ZeekiChen/iWatch/v1.2/CODE/iWatch-v1.2-20201225/User/Page/page_setting.c

#include "iWatch.h"

extern unsigned char xdata main_cache[];
extern unsigned char xdata sub_cache[];

static PageExecuteRate_TypeDef Rate_50hz = {20, 0};

static unsigned char code Text[] = "SETTING";
static unsigned char code Icon[] = {
0x00,0x00,0x00,0x00,0x00,0x00,0x00,0x00,0x00,0x80,0xC0,0xC0,0xC0,0x80,0x00,0x00,
0x00,0x00,0x00,0xE0,0xFC,0xFC,0x1C,0x0C,0x0C,0x1C,0xFC,0xFC,0xC0,0x00,0x00,0x00,
0x00,0x00,0x80,0xC0,0xC0,0xC0,0x80,0x00,0x00,0x00,0x00,0x00,0x00,0x00,0x00,0x00,
0x00,0x00,0x00,0x00,0x00,0x00,0x0C,0x1E,0x7F,0xF7,0xE3,0x81,0x03,0x03,0x07,0x0E,
0x0E,0x07,0x07,0x03,0x83,0x81,0x80,0x80,0x80,0x80,0x81,0x83,0x03,0x07,0x07,0x0E,
0x0E,0x07,0x03,0x03,0x81,0xE3,0xF7,0x7F,0x1E,0x0C,0x00,0x00,0x00,0x00,0x00,0x00,
0x00,0x00,0xF0,0xF0,0x70,0x38,0x38,0x38,0x3E,0x3F,0x0F,0x01,0x00,0x00,0x00,0xF0,
0xFC,0x7E,0x0F,0x07,0xC3,0xE3,0xF1,0x71,0x71,0xF1,0xE3,0xC3,0x07,0x0F,0x7E,0xFC,
0xF0,0x00,0x00,0x00,0x01,0x0F,0x3F,0x3E,0x38,0x38,0x38,0x70,0xF0,0xF0,0x00,0x00,
0x00,0x00,0x0F,0x0F,0x0E,0x0C,0x0C,0x1C,0x7C,0xFC,0xF0,0xC0,0x00,0x00,0x00,0x07,
0x1F,0x3E,0x78,0xF0,0xE1,0xC7,0xC7,0xCE,0xCE,0xC7,0xC7,0xE1,0xE0,0x78,0x3E,0x1F,
0x07,0x00,0x00,0x00,0xC0,0xF0,0xFC,0x7C,0x1C,0x0C,0x0C,0x0E,0x0F,0x0F,0x00,0x00,
0x00,0x00,0x00,0x00,0x00,0x00,0x30,0x7C,0xFE,0xEF,0xC7,0x81,0xC0,0xE0,0xE0,0x70,
0x70,0xF0,0xE0,0xE0,0xC0,0xC1,0x01,0x01,0x01,0x01,0xC1,0xC0,0xE0,0xE0,0xF0,0x70,
0x70,0xE0,0xE0,0xC0,0x81,0xC7,0xEF,0xFE,0x7C,0x30,0x00,0x00,0x00,0x00,0x00,0x00,
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
		0x00,0x00,0x10,0x11,0x16,0x10,0x10,0xF0,0x10,0x10,0x14,0x13,0x10,0x00,0x00,0x00,
		0x10,0x10,0xD0,0xFF,0x90,0x10,0x00,0xFE,0x02,0x02,0x02,0xFE,0x00,0x00,0x00,0x00,
		0x00,0x80,0x80,0x80,0x80,0x80,0x80,0x80,0x80,0x80,0x80,0x80,0x80,0x80,0x00,0x00,
		0x00,0x00,0x00,0x00,0x00,0x00,0x00,0x00,0x00,0x00,0x00,0x00,0x00,0x00,0x00,0x00,
		0x81,0x81,0x41,0x41,0x21,0x11,0x0D,0x03,0x0D,0x11,0x21,0x41,0x41,0x81,0x81,0x00,
		0x04,0x03,0x00,0xFF,0x00,0x83,0x60,0x1F,0x00,0x00,0x00,0x3F,0x40,0x40,0x78,0x00,
		0x00,0x00,0x00,0x00,0x00,0x00,0x00,0x00,0x00,0x00,0x00,0x00,0x00,0x00,0x00,0x00
		/* (64 X 16 )*/
	}
};
#define	MENU_MAX_INDEX	sizeof(SETTINGMENU)/(64*16/8)
static unsigned char code TICK_CROSS[2][32] = {
	{
		0x00,0x0C,0x1E,0x3E,0x7C,0xF8,0xF0,0xE0,0xE0,0xF0,0xF8,0x7C,0x3E,0x1E,0x0C,0x00,
		0x00,0x38,0x7C,0x7E,0x3F,0x1F,0x0F,0x07,0x07,0x0F,0x1F,0x3E,0x7C,0x78,0x30,0x00
		/* (16 X 16 )*/
	},
	{
		0x00,0x80,0xC0,0x80,0x00,0x00,0x00,0x00,0x80,0xC0,0xE0,0xF0,0xF8,0xFC,0x7C,0x38,
		0x03,0x07,0x0F,0x1F,0x3F,0x7E,0x7E,0x3F,0x1F,0x0F,0x07,0x03,0x01,0x00,0x00,0x00
		/* (16 X 16 )*/
	}
};

void SetTime(void);

extern iWatch_config config;	//设置信息结构体
static char menu_first_index = 0;
static char menu_now_index = 0;
static bit selected = 0;
static selected_index = 0;

#define	SWITCH	0
#define	NUM			1
#define	EXE			2
typedef void(*SettingExecute_t)(unsigned char);
typedef void(*SettingExecute)(void);
typedef struct {
	unsigned char *item_content;		//设置项目的文本/图片的指针
	unsigned char control_type;			//设置的类型，NUM:更改数值，SWITCH:开关型，EXE:直接执行型
	unsigned char *value;						//被设置的值的指针
	SettingExecute_t SettingExe_t;	//有一个参数的执行函数，NUM和SWITCH设置类型的属性
	SettingExecute	 SettingExe;		//没有参数的执行函数，EXE设置类型才有的属性
	unsigned char step;							//NUM设置类型的数值步进长度
	unsigned char value_max;					//NUM设置类型的数值最大值
	unsigned char value_min;					//NUM设置类型的数值最小值
	unsigned char *unit;						//被设置的值的单位字符串的指针，NUM设置类型才有的属性
}Setting_TypeDef;
static Setting_TypeDef menu_item[] = {
	{SETTINGMENU[0], EXE, 	 0, 0,										SetTime},
	{SETTINGMENU[1], NUM, 	 0, 0,										0,							1,  20,  5,  "s"},
	{SETTINGMENU[2], NUM, 	 0,	ScreenSetBrightness,	0,							10, 100, 10, "%"},
	{SETTINGMENU[3], SWITCH, 0, 0,										0},
	{SETTINGMENU[4], SWITCH, 0, 0,										0},
	{SETTINGMENU[5], SWITCH, 0,	ScreenSetInverse,			0},
	{SETTINGMENU[6], SWITCH, 0,	EnableBuzzer,					0},
	{SETTINGMENU[7], EXE,		 0,	0, 										MCUSoftReset},
	{SETTINGMENU[8], EXE, 	 0, 0,										iWatchPowerDown}
};		

/**
  * @brief  页面初始化事件
  * @param  无
  * @retval 无
  */
static void Setup()
{
	unsigned char i;
	ClearCache(sub_cache);
	menu_item[1].value = &config.t_inactive_max;
	menu_item[2].value = &config.screen_brightness;
	menu_item[3].value = &config.wrist_up_wake;
	menu_item[4].value = &config.always_on_disp;
	menu_item[5].value = &config.screen_inverse;
	menu_item[6].value = &config.key_sound;
	for(i = 0; i < 4; i++)
	{
		BMPToCache(16, i * 2, 64, 16, menu_item[menu_first_index + i].item_content, sub_cache, COVER);
	}
	PageOpenAnim(ANIM_RIGHT);
}
/**
  * @brief  页面退出事件
  * @param  无
  * @retval 无
  */
static void Exit()
{
	iWatchSaveConfig(&config);
	PageCloseAnim(ANIM_RIGHT);
}
/**
  * @brief  页面循环执行的内容
  * @param  无
  * @retval 无
  */
static void Loop()
{	unsigned char i;
	unsigned char str[5];
	if(PageExecuteRate(&Rate_50hz) == 1)
	{
		ClearCache(main_cache);
		for(i = 0; i < 4; i++)
		{
			BMPToCache(16, i * 2, 64, 16, menu_item[menu_first_index + i].item_content, main_cache, COVER);
			if(menu_item[menu_first_index + i].control_type == SWITCH)
				BMPToCache(96, i * 2, 16, 16, TICK_CROSS[*menu_item[menu_first_index + i].value], main_cache, COVER);
			else if(menu_item[menu_first_index + i].control_type == NUM)
			{
				sprintf(str, "%d%s", (int)(*menu_item[menu_first_index + i].value), (char*)menu_item[menu_first_index + i].unit);
				ShowString(96, i * 2, str, main_cache, FONT8X16, (selected&&selected_index==menu_first_index + i)?INVERSED:NO_INVERSED);
			}
		}
		ShowString(0, (menu_now_index - menu_first_index) * 2, ">", main_cache, FONT8X16, NO_INVERSED);
		ScreenRefreshAll(main_cache);
	}
	
}
/**
  * @brief  页面事件
  * @param  btn:发出事件的按键
  * @param  event:事件编号
  * @retval 无
  */
static void Event(unsigned char event)
{
	if(!selected)
	{
		if(event == KEY1)
			PageShift(page_menu);
		else if(event == KEY2)
		{
			if(--menu_now_index >= 0)
			{
				if(menu_now_index < menu_first_index)
					menu_first_index--;
			}
			else
				menu_now_index = 0;
		}
		else if(event == KEY3)
		{
			if(++menu_now_index < MENU_MAX_INDEX)
			{
				if(menu_now_index > menu_first_index + 3)
					++menu_first_index;
			}
			else
				menu_now_index = MENU_MAX_INDEX - 1;
		}
		else if(event == DOUBLE_TAP)
		{
			if(menu_item[menu_now_index].control_type == SWITCH)
			{
				*menu_item[menu_now_index].value = !*menu_item[menu_now_index].value;
				if(menu_item[menu_now_index].SettingExe_t != 0)
					menu_item[menu_now_index].SettingExe_t(*menu_item[menu_now_index].value);
			}
			else if(menu_item[menu_now_index].control_type == EXE)
			{
				if(menu_item[menu_now_index].SettingExe != 0)
					menu_item[menu_now_index].SettingExe();
			}
			else if(menu_item[menu_now_index].control_type == NUM)
			{
				selected = 1;
				selected_index = menu_now_index;
			}
		}
	}
	else
	{
		if(event == KEY1)
			selected = 0;
		else if(event == KEY2)
		{
			*menu_item[menu_now_index].value += menu_item[menu_now_index].step;
			if(*menu_item[menu_now_index].value >= menu_item[menu_now_index].value_max)
				*menu_item[menu_now_index].value = menu_item[menu_now_index].value_max;
		}
		else if(event == KEY3)
		{
			*menu_item[menu_now_index].value -= menu_item[menu_now_index].step;
			if(*menu_item[menu_now_index].value <= menu_item[menu_now_index].value_min)
				*menu_item[menu_now_index].value = menu_item[menu_now_index].value_min;
		}
		if(menu_item[menu_now_index].SettingExe_t != 0)
			menu_item[menu_now_index].SettingExe_t(*menu_item[menu_now_index].value);
	}
}

void PageRegister_page_setting(unsigned char pageID)
{
	PageRegister(pageID, Text, Icon, Setup, Loop, Exit, Event);
}
void SetTime(void)
{
	PageShift(page_settime);
}
