ZeekiChen/iWatch/v1.2/CODE/iWatch-v1.2-20201225/User/Page/page_bme280.c

#include "iWatch.h"

extern unsigned char xdata main_cache[];
extern unsigned char xdata sub_cache[];

static PageExecuteRate_TypeDef Rate_50hz = {20, 0};

static unsigned char code Text[] = "BME280";
static unsigned char code Icon[] = {
0x00,0x00,0x00,0x00,0x00,0xE0,0x70,0x10,0x18,0x18,0x18,0x10,0x70,0xE0,0x00,0x00,
0x00,0x00,0x00,0x00,0x00,0x00,0x30,0x60,0xC0,0x80,0x00,0x08,0xB8,0x80,0x80,0xC0,
0xDF,0xCE,0xC0,0x80,0x90,0x38,0x08,0x00,0xC0,0xE0,0x70,0x20,0x00,0x00,0x00,0x00,
0x00,0x00,0x00,0x00,0xFF,0xFF,0x98,0x98,0x18,0x18,0x18,0x00,0x00,0xFF,0xFF,0x00,
0x00,0x00,0xC0,0xC0,0xC4,0xC4,0x0C,0x00,0xF0,0xFC,0x0E,0x03,0x01,0x01,0x00,0x00,
0x00,0x00,0x00,0x00,0x01,0x03,0x07,0x0E,0xF8,0xE0,0x04,0x8C,0xC6,0xC0,0xC0,0x80,
0x00,0x00,0x00,0x00,0xFF,0xFF,0x73,0x73,0x00,0x00,0x00,0x00,0x00,0xFF,0xFF,0x00,
0x00,0x00,0x00,0x00,0x18,0x18,0x08,0x80,0xC3,0x8F,0x18,0x30,0x60,0x40,0xC0,0xC0,
0xC0,0xC0,0xC0,0xC0,0x60,0x60,0x30,0x1C,0xCF,0x81,0x08,0x08,0x18,0x00,0x00,0x00,
0x00,0x00,0x00,0x80,0xFF,0x7F,0x0E,0x0E,0x00,0x00,0x00,0x00,0x00,0x7F,0xFF,0x80,
0x00,0x00,0x00,0x00,0x00,0x00,0x03,0x03,0x01,0x00,0x00,0x0C,0x0E,0x00,0x00,0x00,
0x3C,0x3C,0x00,0x00,0x02,0x0E,0x00,0x00,0x00,0x01,0x03,0x02,0x00,0x00,0x00,0x00,
0xF0,0xFE,0x07,0x01,0x00,0x00,0x00,0x00,0x00,0x00,0x00,0x00,0x00,0xC0,0x40,0x01,
0x03,0x1E,0xF8,0x00,0x00,0x00,0x00,0x00,0x00,0x00,0x00,0x00,0x00,0x00,0x00,0x00,
0x00,0x00,0x00,0x00,0x00,0x00,0x00,0x00,0x00,0x00,0x00,0x00,0x00,0x00,0x00,0x00,
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
}
/**
  * @brief  页面循环执行的内容
  * @param  无
  * @retval 无
  */
static void Loop()
{
	if(PageExecuteRate(&Rate_50hz) == 1)
	{
		BME280GetSensorData(&BME280);					//读BME280测量数据并显示
		altitude = 44330.77 * (1 - pow((BME280.pressure / 101500), 0.190263));
		ClearCache(main_cache);
		BMPToCache(0, 0, 48, 64, T_H_P_A, main_cache, 0);
		sprintf(str1, "%.1f", BME280.temperature);
		ShowString(48, 0, str1, main_cache, FONT8X16, NO_INVERSED);
		BMPToCache(84, 0, 16, 16, CELSIUS_ICON, main_cache, 0);
		sprintf(str1, "%.1f %%", BME280.humidity);
		ShowString(48, 2, str1, main_cache, FONT8X16, NO_INVERSED);
		sprintf(str1, "%ld Pa", (long)BME280.pressure);
		ShowString(48, 4, str1, main_cache, FONT8X16, NO_INVERSED);
		sprintf(str1, "%d m", (int)altitude);
		ShowString(48, 6, str1, main_cache, FONT8X16, NO_INVERSED);
		ScreenRefreshAll(main_cache);
	}
}
/**
  * @brief  页面事件
  * @param  btn:发出事件的按键
  * @param  event:事件编号
  * @retval 无
  */
static void Event(unsigned char event)
{
	if(event == KEY1)
		PageShift(page_menu);
}

void PageRegister_page_bme280(unsigned char pageID)
{
	PageRegister(pageID, Text, Icon, Setup, Loop, Exit, Event);
}
