ZeekiChen/iWatch/v1.2/CODE/iWatch-v1.2-20201225/User/Sensor/Ellipsoid fitting.c

#include "Ellipsoid fitting.h"
#include "stdio.h"
#include "string.h"
#include "math.h"

#define MATRIX_SIZE 6
//#define u8 unsigned char
float m_matrix[MATRIX_SIZE][MATRIX_SIZE + 1];	//系数矩阵
float final_solve[MATRIX_SIZE] = { 0 };				//方程组的解对应最小二乘椭球拟合中的，a，b，c，d，e，f，

float m_result[MATRIX_SIZE];
int N = 0;//计算累计的采样点次数的

//取绝对值
float Abs(float a)
{
	return a < 0 ? -a : a;
}

//把矩阵系数全部清除为0
void ResetMatrix(void)
{
	unsigned char row, column;
	for (row = 0; row < MATRIX_SIZE; row++)
	{
		for (column = 0; column < MATRIX_SIZE + 1; column++)
			m_matrix[row][column] = 0.0f;
	}
}

//把输入的数据先生成矩阵的元素的总和
void CalcData_Input(float x, float y, float z)
{
	float V[MATRIX_SIZE + 1];
	unsigned char row, column;
	N++;
	V[0] = y*y;
	V[1] = z*z;
	V[2] = x;
	V[3] = y;
	V[4] = z;
	V[5] = 1.0;
	V[6] = -x*x;
	//构建系数矩阵，并进行累加
	for (row = 0; row < MATRIX_SIZE; row++)
	{
		for (column = 0; column < MATRIX_SIZE + 1; column++)
		{
			m_matrix[row][column] += V[row] * V[column];
		}
	}
	//b向量是m_matrix[row][6]
}

//化简系数矩阵，把除以N带上
void CalcData_Input_average()
{
	unsigned char row, column;
	for (row = 0; row < MATRIX_SIZE; row++)
		for (column = 0; column < MATRIX_SIZE + 1; column++)
			m_matrix[row][column] /= N;
	//b向量是m_matrix[row][6]
}
//显示出来系数矩阵和增广矩阵[A|b]
/*
void DispMatrix(void)
{
	unsigned char row, column;
	for (row = 0; row < MATRIX_SIZE; row++)
	{
		for (column = 0; column < MATRIX_SIZE + 1; column++)
		{
			printf("%23f ", m_matrix[row][column]);
			if (column == MATRIX_SIZE - 1)
				printf("|");
		}
		printf("\r\n");
	}
	printf("\r\n\r\n");
}
*/
//交换两行元素位置
void Row2_swop_Row1(int row1, int row2)
{
	float tmp = 0;
	unsigned char column;
	for (column = 0; column < MATRIX_SIZE + 1; column++)
	{
		tmp = m_matrix[row1][column];
		m_matrix[row1][column] = m_matrix[row2][column];
		m_matrix[row2][column] = tmp;
	}
}

//用把row行的元素乘以一个系数k
void k_muiltply_Row(float k, int row)
{
	unsigned char column;
	for (column = 0; column < MATRIX_SIZE + 1; column++)
		m_matrix[row][column] *= k;
}

//用一个数乘以row1行加到row2行上去
void Row2_add_kRow1(float k, int row1, int row2)
{
	unsigned char column;
	for (column = 0; column < MATRIX_SIZE + 1; column++)
		m_matrix[row2][column] += k*m_matrix[row1][column];
}


//列主元，第k次消元之前，把k行到MATRIX_SIZE的所有行进行冒泡排出最大，排序的依据是k列的元素的大小
void MoveBiggestElement_to_Top(int k)
{
	int row = 0, column = 0;
	for (row = k + 1; row < MATRIX_SIZE; row++)
	{
		if (Abs(m_matrix[k][k]) < Abs(m_matrix[row][k]))
		{
			Row2_swop_Row1(k, row);
		}
	}
}

//高斯消元法，求行阶梯型矩阵
unsigned char Matrix_GaussElimination(void)
{
	float k = 0;
	unsigned char cnt,row;
	for (cnt = 0; cnt < MATRIX_SIZE; cnt++)//进行第k次的运算，主要是针对k行以下的行数把k列的元素都变成0
	{
		//把k行依据k列的元素大小，进行排序
		MoveBiggestElement_to_Top(cnt);
		if (m_matrix[cnt][cnt] == 0)
			return(1);			//返回值表示错误
		//把k行下面的行元素全部消成0，整行变化
		for (row = cnt + 1; row < MATRIX_SIZE; row++)
		{
			k = -m_matrix[row][cnt] / m_matrix[cnt][cnt];
			Row2_add_kRow1(k, cnt, row);
		}
		//DispMatrix();
	}
	return 0;
}

//求行最简型矩阵，即把对角线的元素全部化成1
void Matrix_RowSimplify(void)
{
	float k = 0;
	unsigned char row;
	for (row = 0; row < MATRIX_SIZE; row++)
	{
		k = 1 / m_matrix[row][row];
		k_muiltply_Row(k, row);
	}
	//DispMatrix();
}

//求非齐次线性方程组的解
void Matrix_Solve(float *solve)
{
	long row;
	unsigned char column;
	for (row = MATRIX_SIZE - 1; row >= 0; row--)
	{
		solve[row] = m_matrix[row][MATRIX_SIZE];
		for (column = MATRIX_SIZE - 1; column >= row + 1; column--)
			solve[row] -= m_matrix[row][column] * solve[column];
	}
	//printf("  a = %.3f| b = %.3f| c = %.3f| d = %.3f| e = %.3f| f = %.3f ", solve[0], solve[1], solve[2], solve[3], solve[4], solve[5]);
	//printf("\r\n");
	//printf("\r\n");
}

//整个椭球校准的过程
unsigned char Ellipsoid_fitting_Process(struct cal_data *dat)
{
	float a = 0, b = 0, c = 0, d = 0, e = 0, f = 0;
	float X0 = 0, Y0 = 0, Z0 = 0, A = 0, B = 0, C = 0;
	//ResetMatrix();
	//这里输入任意个点加速度参数，尽量在球面上均匀分布
	/*
	CalcData_Input(87, -52, -4454);
	CalcData_Input(301, -45, 3859);
	CalcData_Input(274, 4088, -303);
	CalcData_Input(312, -4109, -305);
	CalcData_Input(-3805, -24, -390);
	CalcData_Input(4389, 6, -228);
	CalcData_Input(261, 2106, -3848);
	CalcData_Input(327, -2047, -3880);
	CalcData_Input(-1963, -13, -3797);
	CalcData_Input(3024, 18, -3449);
	*/
	CalcData_Input_average();				//对输入的数据到矩阵元素进行归一化
	//DispMatrix();										//显示原始的增广矩阵
	if (Matrix_GaussElimination())	//求得行阶梯形矩阵
	{
		printf("the marix could not be solved\r\n");
		return 0;
	}
	else
	{
		Matrix_RowSimplify();				//化行最简形态
		Matrix_Solve(final_solve);	//求解a,b,c,d,e,f
		a = final_solve[0];
		b = final_solve[1];
		c = final_solve[2];
		d = final_solve[3];
		e = final_solve[4];
		f = final_solve[5];

		X0 = -c / 2;
		Y0 = -d / (2 * a);
		Z0 = -e / (2 * b);
		A = sqrt(X0*X0 + a*Y0*Y0 + b*Z0*Z0 - f);
		B = A / sqrt(a);
		C = A / sqrt(b);
		
		dat->X0 = X0;
		dat->Y0 = Y0;
		dat->Z0 = Z0;
		dat->A = A;
		dat->B = B;
		dat->C = C;
		/*
		printf("((x - x0) / A) ^ 2 + ((y - y0) / B) ^ 2 + ((z - z0) / C) ^ 2 = 1 Ellipsoid result as below：\r\n");
		printf("\r\n");
		printf("X0 = %.3f| Y0 = %.3f| Z0 = %.3f| A = %.3f| B = %.3f| C = %.3f \r\n", X0, Y0, Z0, A, B, C);
		*/
		return 1;
	}
}
