ZeekiChen/iWatch/v1.2/CODE/iWatch-v1.2-20201225/User/Display/oled.h

#ifndef __OLED_H
#define __OLED_H

#include "stc8a.h"

#define  u8 unsigned char 
#define  u32 unsigned int 
	
//OLED模式设置
//0:4线串行模式
//1:并行8080模式
#define OLED_MODE 1

#define OLED_CMD  0	//写命令
#define OLED_DATA 1	//写数据

#define OLED_DAT	P0
sbit OLED_RST = P1^1;		//复位
sbit OLED_DC =	P5^3;		//数据/命令控制
sbit OLED_WR =	P5^2;
sbit OLED_RD =	P1^0;
//sbit OLED_CS=P2^0; //片选
#define OLED_RST_Clr() OLED_RST=0
#define OLED_RST_Set() OLED_RST=1

#define OLED_DC_Clr() OLED_DC=0
#define OLED_DC_Set() OLED_DC=1

#define OLED_WR_Clr() OLED_WR=0
#define OLED_WR_Set() OLED_WR=1

#define OLED_RD_Clr() OLED_RD=0
#define OLED_RD_Set() OLED_RD=1


#define XLevelL			0x02
#define XLevelH			0x10
#define Max_Column	128
#define Max_Row			64
#define X_WIDTH 		128
#define Y_WIDTH 		64	    						  
//-----------------OLED端口定义----------------  					   

void delay_ms(unsigned int ms);

//OLED控制用函数
void OLED_WR_Byte(u8 dat,u8 cmd);	    
void OLED_Display_On(void);
void OLED_Display_Off(void);	
void OLED_Set_Brightness(unsigned char brightness);
//void OLED_Horizental_Reverse(unsigned char reverse);
//void OLED_Vertical_Reverse(unsigned char reverse);
void OLED_Inverse(unsigned char k);
void OLED_Init(void);
void OLED_Clear(void);
void OLED_Set_Pos(unsigned char x, unsigned char y);
void OLED_Refresh(unsigned char *buf);


#endif  
	 
